Embebidos-Fran-Marcos-Nacho/tdse-tf_1-2/Diagrama de conexión simplificado/placa desde arriba2.jpeg

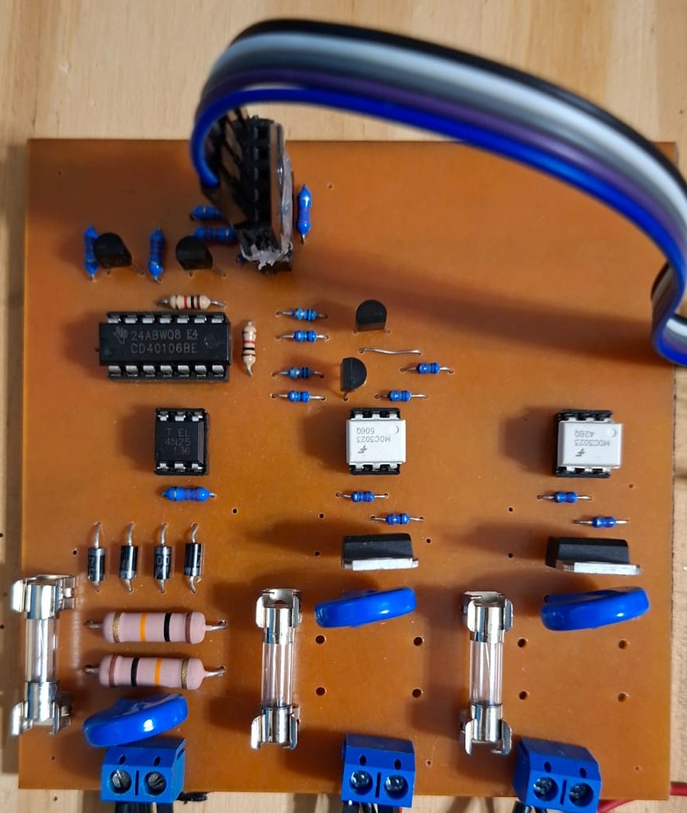
Diagrama de conexión simplificado/placa desde arriba2.jpeg
