Embebidos-Fran-Marcos-Nacho/tdse-tf_1-2/Diagrama de conexión simplificado/placa desde arriba.jpeg

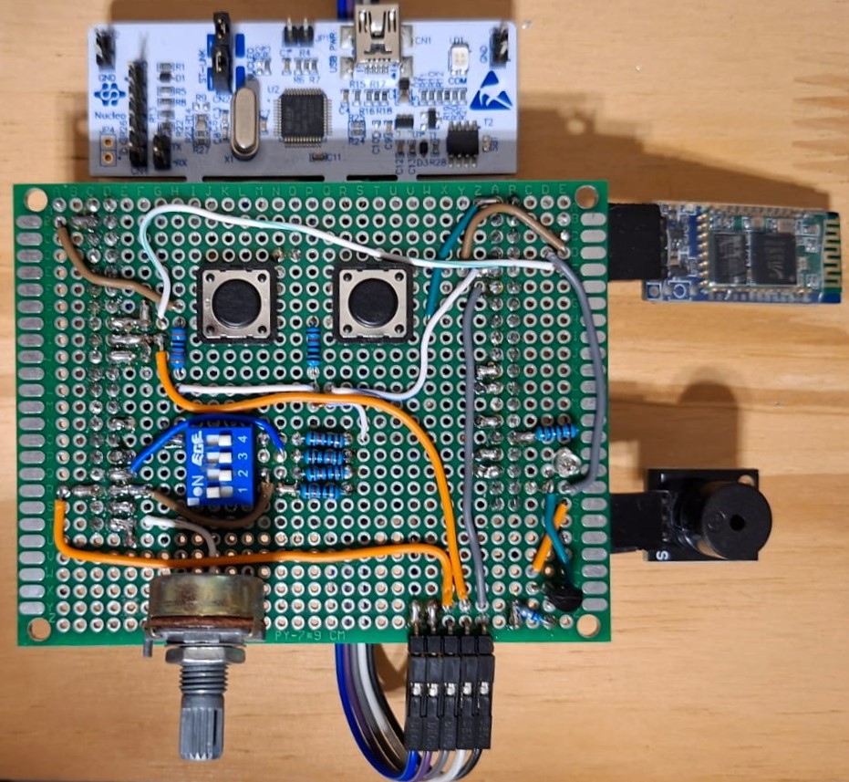
Diagrama de conexión simplificado/placa desde arriba.jpeg
