Embebidos-Fran-Marcos-Nacho/tdse-tf_1-2/Diagrama de conexión simplificado/placa_desde_arriba2-removebg-preview.png

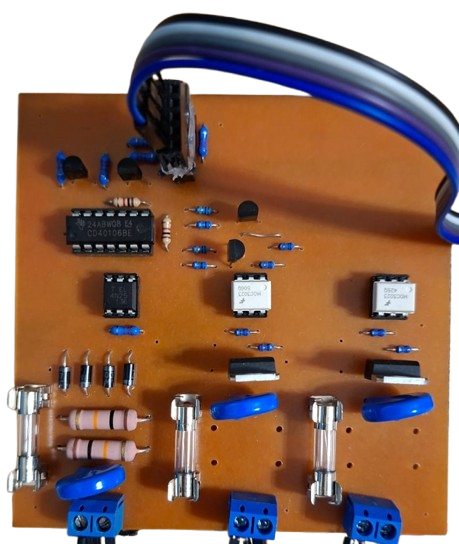
Diagrama de conexión simplificado/placa_desde_arriba2-removebg-preview.png
