Embebidos-Fran-Marcos-Nacho/tdse-tf_1-2/Hardware/bulbo.jpg

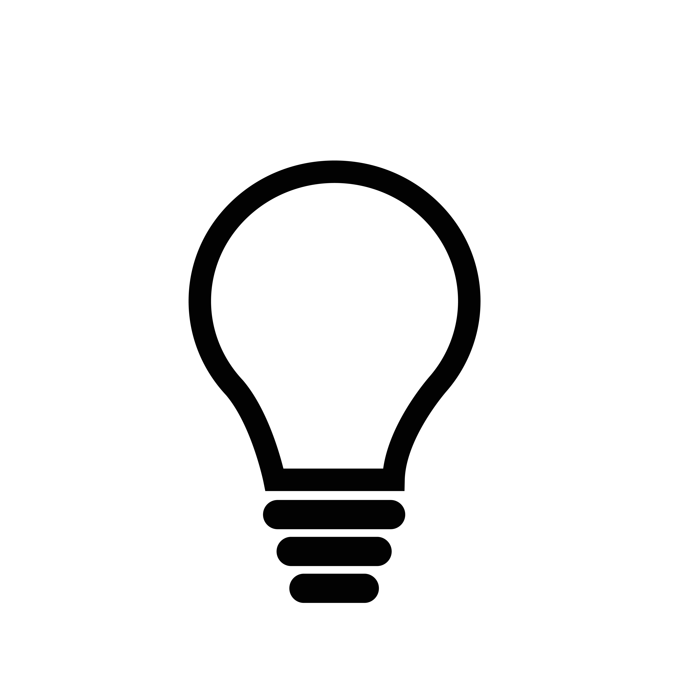
Hardware/bulbo.jpg
