Embebidos-Fran-Marcos-Nacho/tdse-tf_1-2/Hardware/fan.jpg

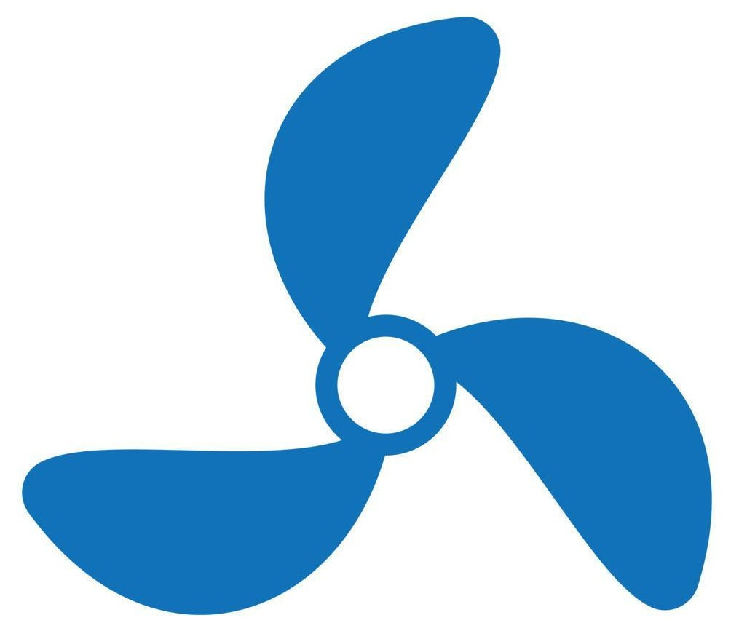
Hardware/fan.jpg
