Embebidos-Fran-Marcos-Nacho/tdse-tf_1-2/Memoria técnica/cosas e imagenes para memoria técnica - hardware/banco de trabajo desprolijo/WhatsApp Image 2026-02-03 at 16.04.08.jpeg

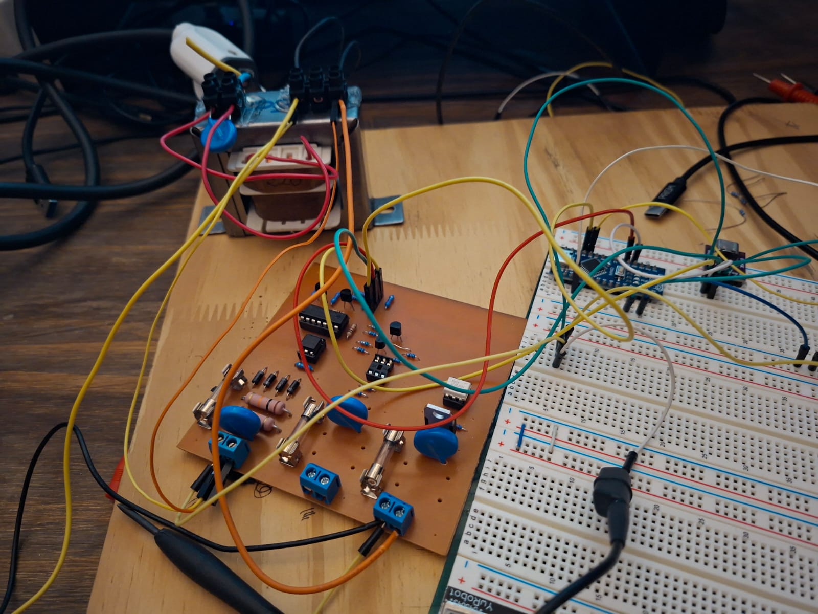
Memoria técnica/cosas e imagenes para memoria técnica - hardware/banco de trabajo desprolijo/WhatsApp Image 2026-02-03 at 16.04.08.jpeg
