Embebidos-Fran-Marcos-Nacho/tdse-tf_1-2/Memoria técnica/cosas e imagenes para memoria técnica - hardware/ZCD/salida del schmitt trigger.jpeg

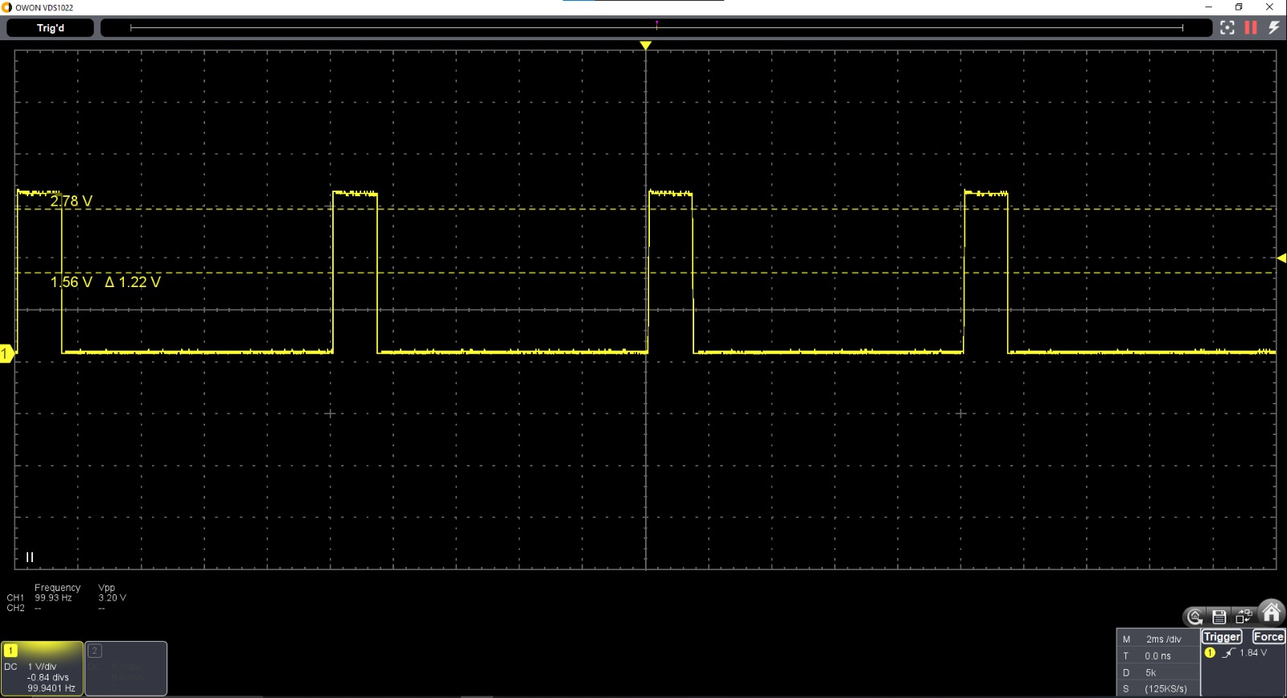
Memoria técnica/cosas e imagenes para memoria técnica - hardware/ZCD/salida del schmitt trigger.jpeg
