Embebidos-Fran-Marcos-Nacho/tdse-tf_1-2/Memoria técnica/cosas e imagenes para memoria técnica - hardware/ZCD/trafo 24vac.jpeg

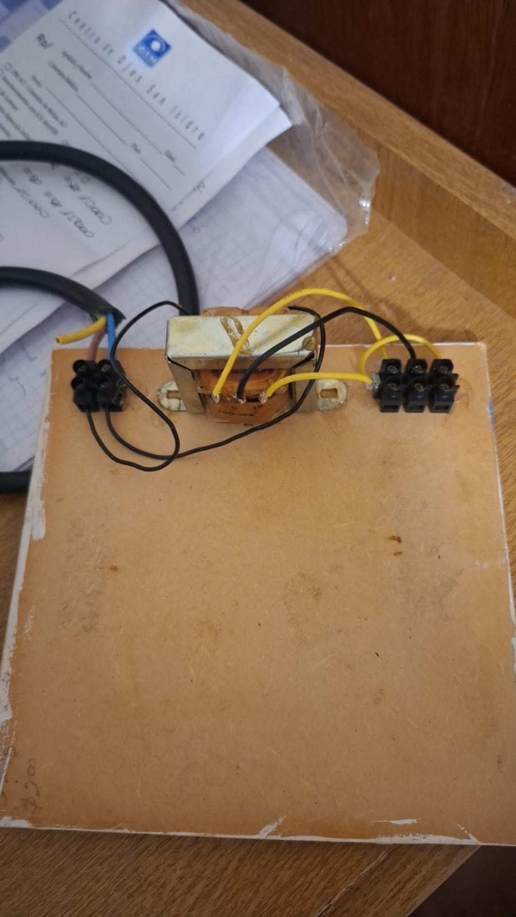
Memoria técnica/cosas e imagenes para memoria técnica - hardware/ZCD/trafo 24vac.jpeg
