Embebidos-Fran-Marcos-Nacho/tdse-tf_1-2/Memoria técnica/imgs/mit app celu.png

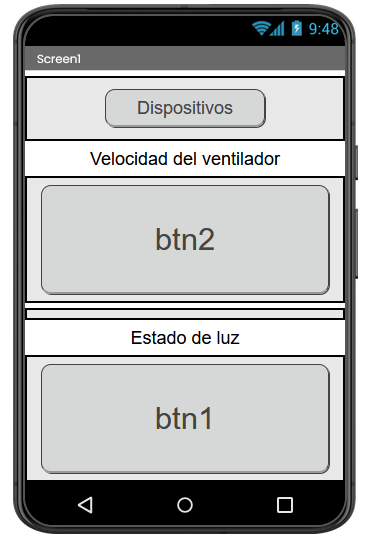
Memoria técnica/imgs/mit app celu.png
