Embebidos-Fran-Marcos-Nacho/tdse-tf_1-2/Hardware/placa dimmer/simus/simu spice.asc

C1: cap; 0.1µ
D1: diode; 1N4007
D2: diode; 1N4007
D3: diode; 1N4007
D4: diode; 1N4007
E1: e; 3.3
M1: nmos; 2N7000
Q1: npn
R1: res; 180
R2: res; 1Meg
R3: res; 5
R4: res; 0
R5: res; 220
R6: res; 0
R7: res; 317
R8: res; 220
R9: res; 2k2
R10: res; 2200
R11: res; 1k
R12: res; 200
R13: res; 2k2
R14: res; 1k
R15: res; 2k2
U1: MOC3023
U2: TRIAC; BTA06-600C
U3: 4N25
U4: delay; t=0.00072
U5: delay; t=5m
U6: RisingEdgeDetector; Tedge=0.1m
U7: cd40106b
U8: cd40106b
U9: cd40106b
V1: voltage; 5v
V2: voltage; 5
V3: voltage; SINE(0 33 50)
Named nets: 0, 5V
.tran 1
.inc st_standard_snubberless_triacs.lib
.model MYSW SW(Ron=0.01 Roff=10Meg Vt=0.5)
Micro
delay que centra
la detección del cruce 
por cero
delay que 
efectua el dimming
arreglo de señal 
proveniente de ZCD
