Embebidos-Fran-Marcos-Nacho/tdse-tf_1-2/Hardware/placa dimmer/simus/level shift.asc

D2: diode
M2: nmos; 2N7000
Q4: npn
R3: res; 1Meg
R6: res; 2k2
R7: res; 2k2
R9: res; 5
R10: res; 180
U1: cd40106b
V3: voltage; 5v
V4: voltage; PULSE(0 3.3 0 0 0 10m 0.1)
Named nets: 0
.tran 1
