Embebidos-Fran-Marcos-Nacho/tdse-tf_1-2/Software STM32/main/app/inc/logger.h

/*
 * Copyright (c) 2023 Sebastian Bedin <sebabedin@gmail.com>.
 * All rights reserved.
 *
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
 * 1. Redistributions of source code must retain the above copyright
 *    notice, this list of conditions and the following disclaimer.
 *
 * 2. Redistributions in binary form must reproduce the above copyright
 *    notice, this list of conditions and the following disclaimer in the
 *    documentation and/or other materials provided with the distribution.
 *
 * 3. Neither the name of the copyright holder nor the names of its
 *    contributors may be used to endorse or promote products derived from
 *    this software without specific prior written permission.
 *
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
 * @file   : logger.h
 * @author : Sebastian Bedin <sebabedin@gmail.com>
 * @version	v1.0.0
 */

#ifndef INC_LOGGER_H_
#define INC_LOGGER_H_

/********************** CPP guard ********************************************/
#ifdef __cplusplus
extern "C" {
#endif

/********************** inclusions *******************************************/

#include <stdio.h>
#include <stdint.h>
#include <stdbool.h>
#include <string.h>

/********************** macros ***********************************************/

#define LOGGER_CONFIG_ENABLE                    (1)
#define LOGGER_CONFIG_MAXLEN                    (192)
#define LOGGER_CONFIG_USE_SEMIHOSTING           (0)
#define LOGGER_CONFIG_USE_UART                  (1)
#define LOGGER_CONFIG_UART_TIMEOUT_MS           (20)

#if 1 == LOGGER_CONFIG_ENABLE
#define LOGGER_LOG(...)                                                      \
    do {                                                                     \
        logger_msg_len = snprintf(logger_msg, (LOGGER_CONFIG_MAXLEN - 1),    \
                                  __VA_ARGS__);                              \
        logger_log_print_(logger_msg);                                       \
    } while (0)
#else
#define LOGGER_LOG(...)
#endif

#define GET_NAME(var)  #var

/********************** typedef **********************************************/

extern char* const logger_msg;
extern int logger_msg_len; // only for debug information

/********************** external functions declaration ***********************/

void logger_log_print_(char* const msg);

/********************** End of CPP guard *************************************/
#ifdef __cplusplus
}
#endif

#endif /* INC_LOGGER_H_ */

/********************** end of file ******************************************/
